Franks3dShop/Amiga2MacFloppy/References/MacInterface/MacPCBSolderside.png

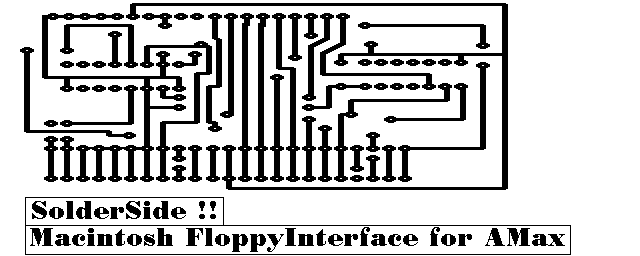
References/MacInterface/MacPCBSolderside.png
